MR-DOS/guitar_down_octave/spice/subharmonic_generator.asc

A1: dflop; Vhigh=5 Vlow=0 Ref=2.5 Trise=5n Tfall=5n Td=5n
C1: cap; 47n
C2: cap; 1n
C3: cap; 100p
C4: cap; 100p
C5: cap; 100n
C6: cap; 10n
C7: cap; 10n
C8: cap; 150n
C9: cap; 10µ
C10: cap; 100n
C11: cap; 100p
C12: cap; 1n
C13: cap; 10n
C14: cap; 1µ
C15: cap; 100n
C16: cap; 100n
C17: cap; 100p
C18: cap; 1n
C19: cap; 100n
C20: cap; 10n
C21: cap; 10n
C22: cap; 100n
C23: cap; 100n
D1: diode; 1N4148
D2: diode; 1N4148
D3: diode; 1N4148
D4: diode; 1N4148
D5: diode; 1N4148
D6: diode; 1N4148
D7: diode; 1N4148
D8: diode; 1N4148
D9: diode; 1N4148
D10: diode; 1N4148
D11: diode; 1N4148
D12: diode; 1N4148
E1: e; 1
E3: e; 1
E4: e; 1
R1: res; 10k
R2: res; 1k
R3: res; 330k
R4: res; 2k
R5: res; 10k
R6: res; 1k
R7: res; 470
R8: res; 470
R9: res; 4k7
R10: res; 47
R11: res; 4k
R12: res; 1k
R13: res; 10k
R14: res; 10k
R15: res; 10k
R16: res; 2k2
R17: res; 2k2
R18: res; 3k9
R19: res; 3k3
R20: res; 47
R21: res; 68k
R22: res; 1k
R23: res; 3k3
R24: res; 100k
R25: res; 68k
R26: res; 330
R27: res; 330
R28: res; 10k
R29: res; 2k2
R30: res; 4k4
R31: res; 1k
R32: res; 18k
R33: res; 4k7
R34: res; 2k2
R35: res; 2k2
R36: res; 3k9
R37: res; 1k
R38: res; 3k3
R39: res; 4.7
R40: res; 3k3
R41: res; 1k
R42: res; 1k5
R43: res; 220k
R44: res; 1k
R45: res; 4k7
R46: res; 220k
R47: res; 4.7
R48: res; 1k
R49: res; 1k
R50: res; 1k
R51: res; 4k7
R52: res; 22k
R53: res; 2k7
R54: res; 47k
R55: res; 22k
R56: res; 47k
R57: res; 47k
R58: res; 100
R59: res; 680k
R60: res; 4.7
R61: res; 47k
R62: res; 100
R63: res; 680k
R64: res; 220k
R65: res; 4k7
R66: res; 4k7
R67: res; 220k
R68: res; 1k
R69: res; 1k
R70: res; 1k
R71: res; 4k7
R72: res; 4.7
S1: sw; MYSW
S2: sw; MYSW
S3: sw; MYSW
S4: sw; MYSW
S5: sw; MYSW
S6: sw; MYSW
U1: UniversalOpamp2
U2: UniversalOpamp2
U3: UniversalOpamp2
U4: UniversalOpamp2
U6: UniversalOpamp2
U7: UniversalOpamp2
U8: UniversalOpamp2
U9: UniversalOpamp2
U10: UniversalOpamp2
U11: lf398; LF398J
U12: UniversalOpamp2
U13: UniversalOpamp2
U14: lf398; LF398J
U15: UniversalOpamp2
U16: UniversalOpamp2
U17: UniversalOpamp2
U18: UniversalOpamp2
U19: UniversalOpamp2
U20: UniversalOpamp2
V1: voltage; SINE(0 0.04 220 20m); AC 1
V2: voltage; 12
V3: voltage; 12
V4: voltage; 5
V5: voltage; -5
V6: voltage; SINE(0 0.002 660 20m); AC 1
V7: voltage; SINE(0 0.0005 1100 20m); AC 1
V8: voltage; SINE(0 0.0005 1540 20m); AC 1
X1: gilbert
X2: gilbert
Named nets: 0, +V, -V, +5, vref, clk, wet, half-wet, nclk, lref, derivation, extreme, -5, AGC
.tran 0 800m 30m 100u startup
.model MYSW SW(Ron=50 Roff=1Meg Vt=0 Vh=0)
.include lf398.sub
30 Hz notch filter to prevent LF saturation of phasing circuit
Input amplifier, the gain should be modified with respect to real guitar
90° phasing circuit, works from about 60+ Hz
Zero derivation detection circuit, U1 has to be replaced with comparator
Synchronous  peak detector
Amplifier compensating the switch resistance
AGC circuit, sets gain so that output amplitude corresponds to input amplitude using the detected peak voltage
Square-root circuit, uses logarithmic amplifier, division by 2 and exponentiator
Switches which switch polarity of the sine wave
Filter to filter out part of the polarity switching distortion
reference voltage for the switches, has no meaning for real circuit
.four 110Hz 150 -1 V(wet)
.OPTIONS plotwinsize=0
.OPTIONS numdgt=7
